balmerdx/RLCMeterH750/h7code/Src/settings.h

#pragma once

#define FLASH_SECTOR_SETTINGS 0
#define FLASH_SECTOR_CORRECTION 1

#define CORRECTION_COUNT 3

typedef enum GraphType
{
    GRAPH_Z_RE,
    GRAPH_Z_IM,
    GRAPH_Z_RE_Z_IM,
    GRAPH_Z_PHASE,
    GRAPH_Z_L,
    GRAPH_Z_C,
} GraphType;

typedef enum
{
    VM_LC,
    VM_Z_REAL_IMAG,
    VM_Z_ABS_ARG,
} VIEW_MODE;

typedef struct Settings
{
    bool view_parallel;
    //all_frequencies==true - все частоты из StandartFreq
    //all_frequencies==false - небольшое количество частот из StandartFreq (чтобы быстро листалось)
    bool all_frequencies;
    VIEW_MODE view_mode;

    //Индекс, для StandartFreq функции
    int single_freq_index;

    int32_t graph_min_freq;
    int32_t graph_max_freq;
    GraphType graph_type;

    //Индекс таблицы для коррекции
    int correction_index;
} Settings;

extern Settings g_settings;

extern char* g_correction_names[CORRECTION_COUNT];

void LoadSettings();
bool SaveSettingsIfChangedAndTimeUp();
