balmerdx/RLCMeterH750/h7code/Src/hardware/delay.h

#pragma once

//Точность +-1 uS
void DelayInit();
void DelayDeinit();
//max 0xFFFF=0.1 секунда

#define DELAY_US_MAX 0xFFFFF
void DelayUs(uint16_t countUs);
static inline uint16_t TimeUs() { return TIM15->CNT; }

void DelayMs(uint32_t ms);
uint32_t TimeMs();
